stingray127/handwirehotswap/img/matrix/col/0.jpg

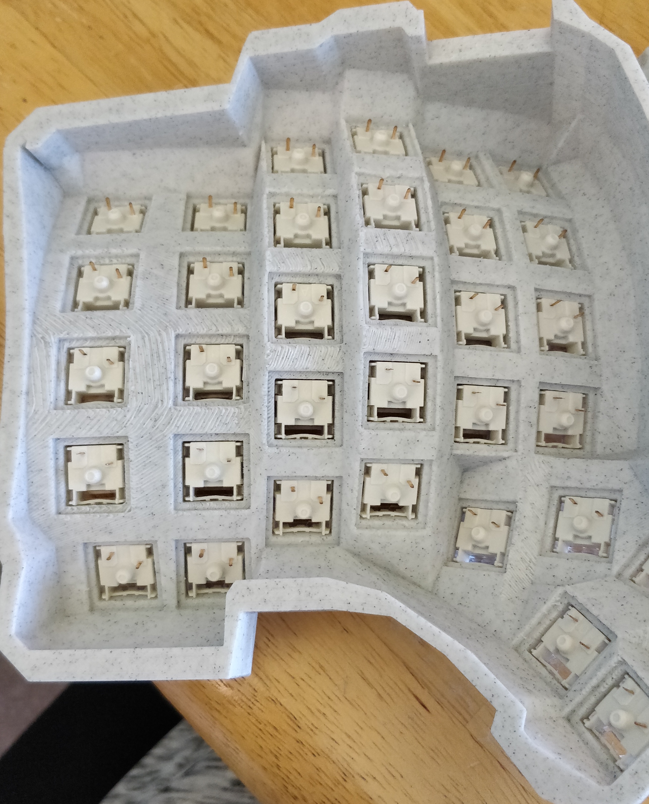
img/matrix/col/0.jpg
