stingray127/handwirehotswap/img/matrix/col/1.jpg

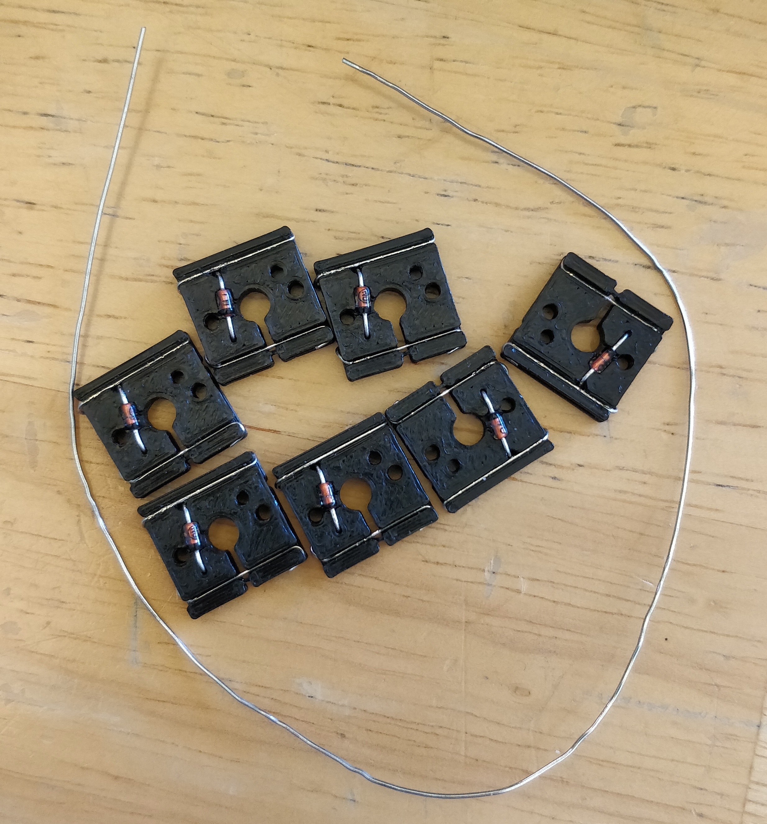
img/matrix/col/1.jpg
