stingray127/handwirehotswap/img/matrix/col/2.jpg

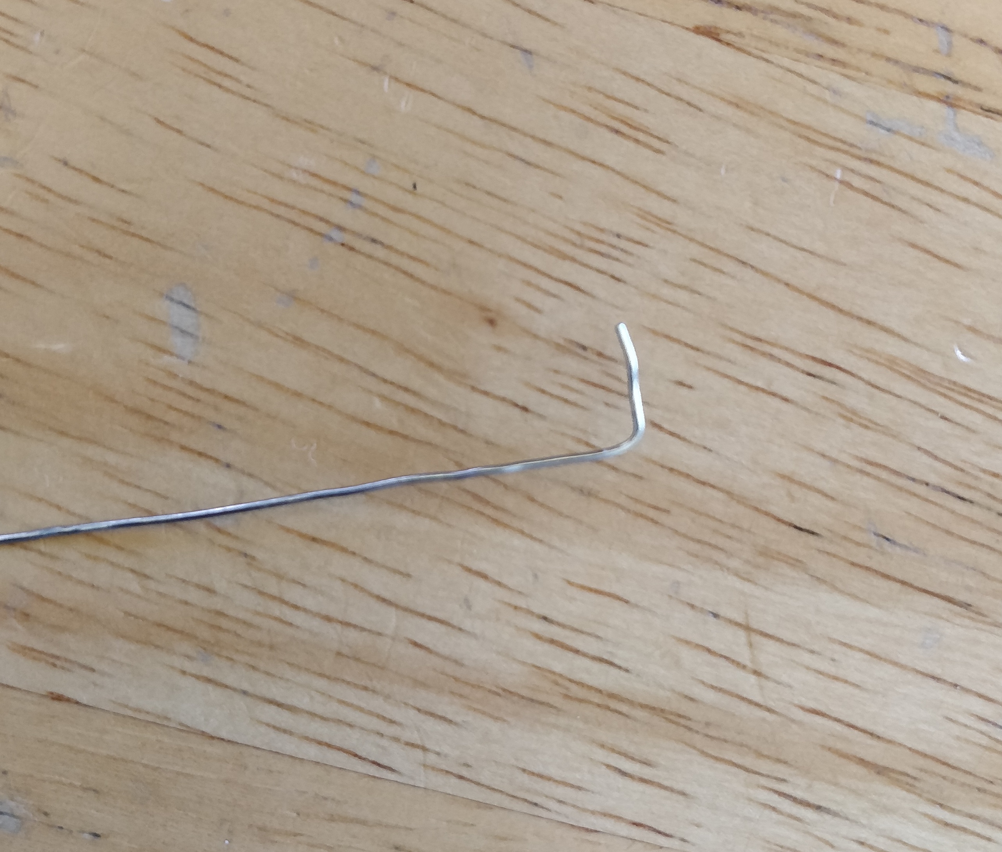
img/matrix/col/2.jpg
