stingray127/handwirehotswap/img/matrix/col/3.jpg

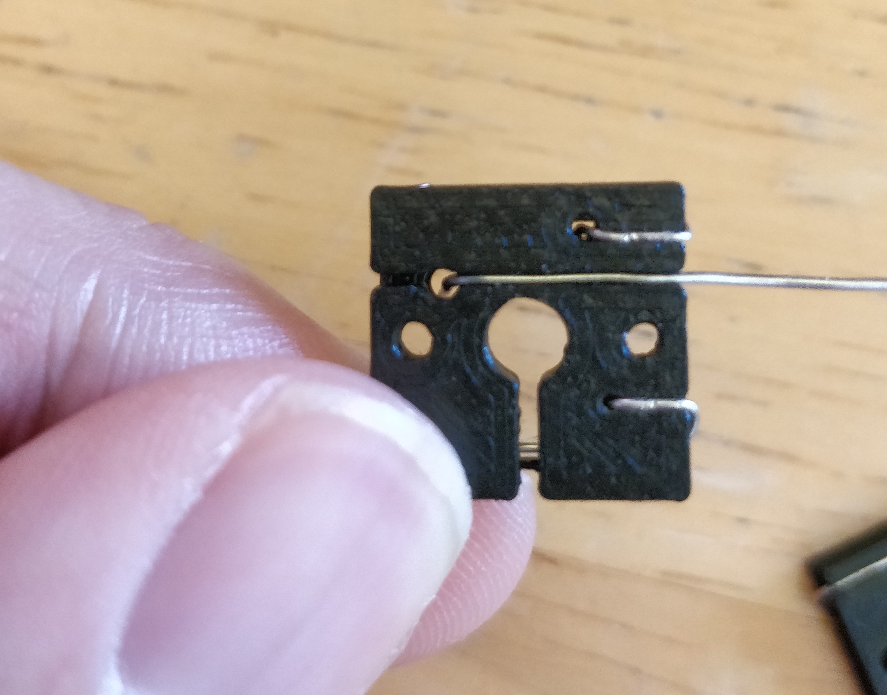
img/matrix/col/3.jpg
