stingray127/handwirehotswap/img/matrix/col/4.jpg

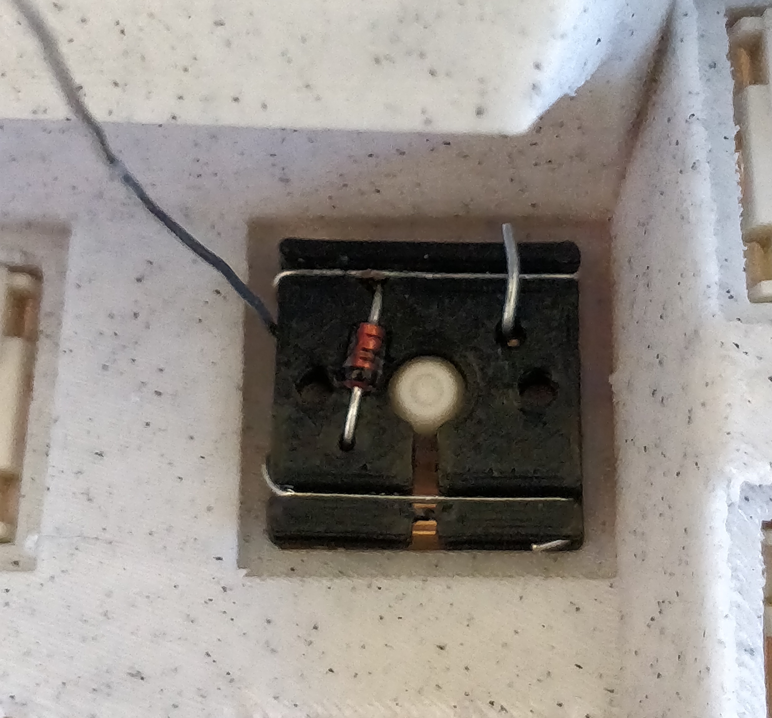
img/matrix/col/4.jpg
