stingray127/handwirehotswap/img/matrix/col/5.jpg

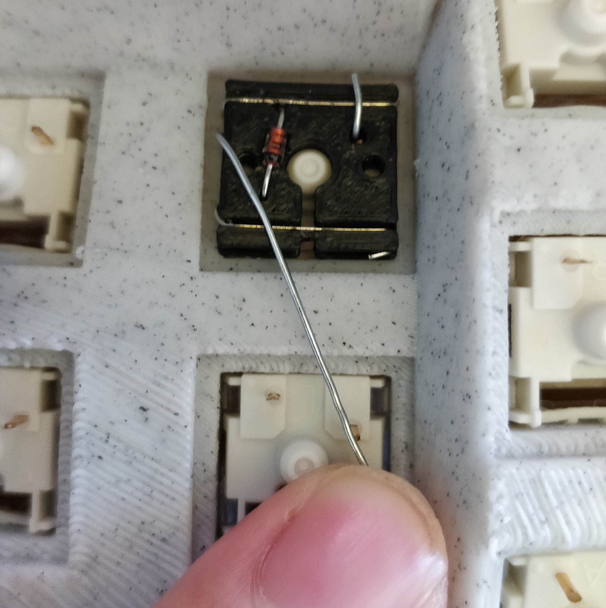
img/matrix/col/5.jpg
