stingray127/handwirehotswap/img/matrix/col/6.jpg

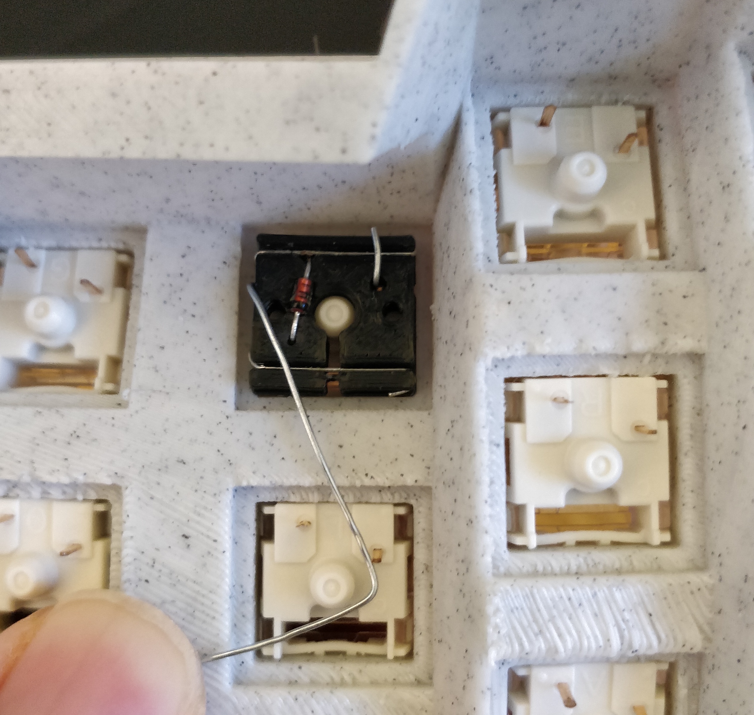
img/matrix/col/6.jpg
