stingray127/handwirehotswap/img/matrix/col/7.jpg

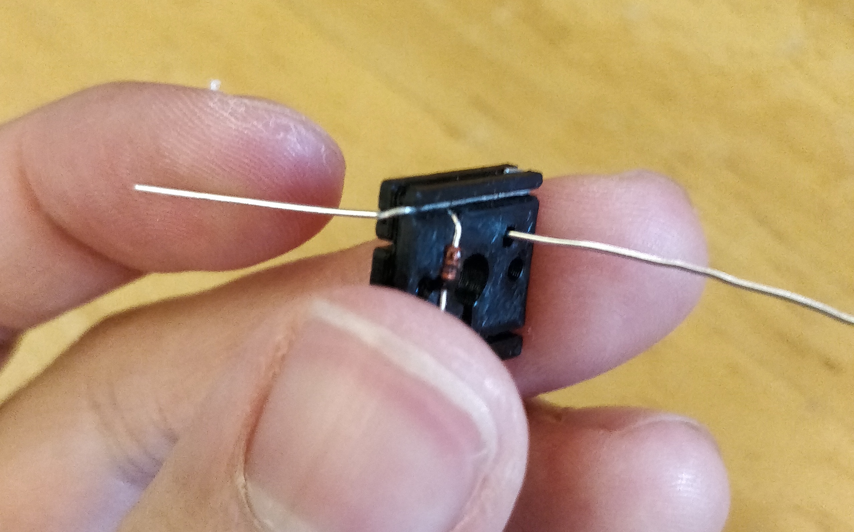
img/matrix/col/7.jpg
