stingray127/handwirehotswap/img/matrix/col/8.jpg

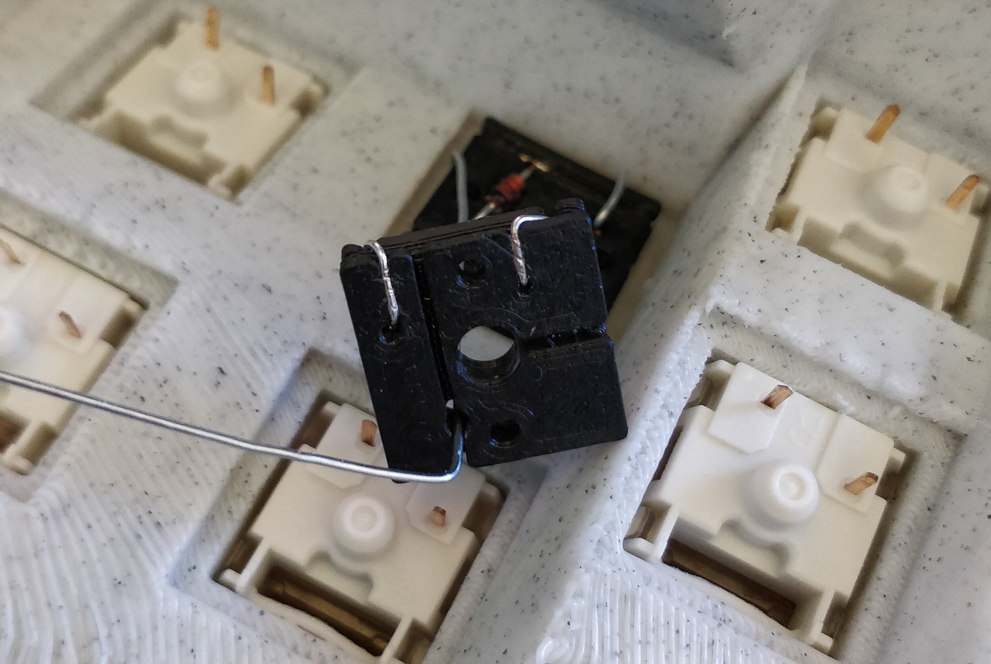
img/matrix/col/8.jpg
