stingray127/handwirehotswap/img/matrix/col/9.jpg

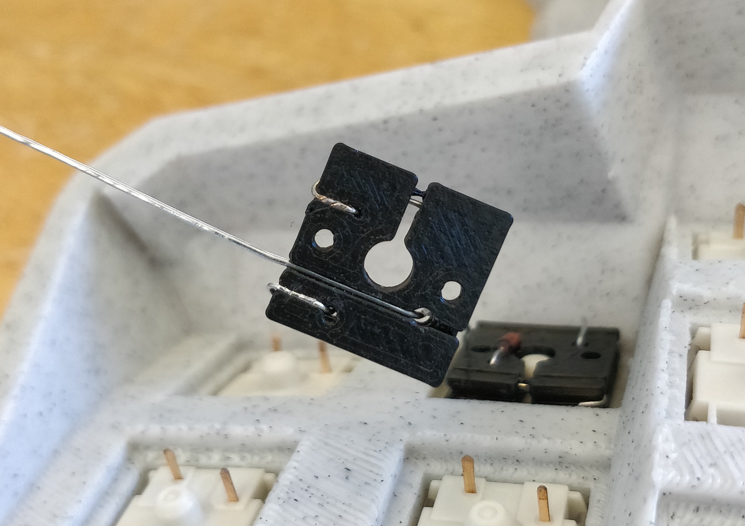
img/matrix/col/9.jpg
