stingray127/handwirehotswap/img/matrix/col/10.jpg

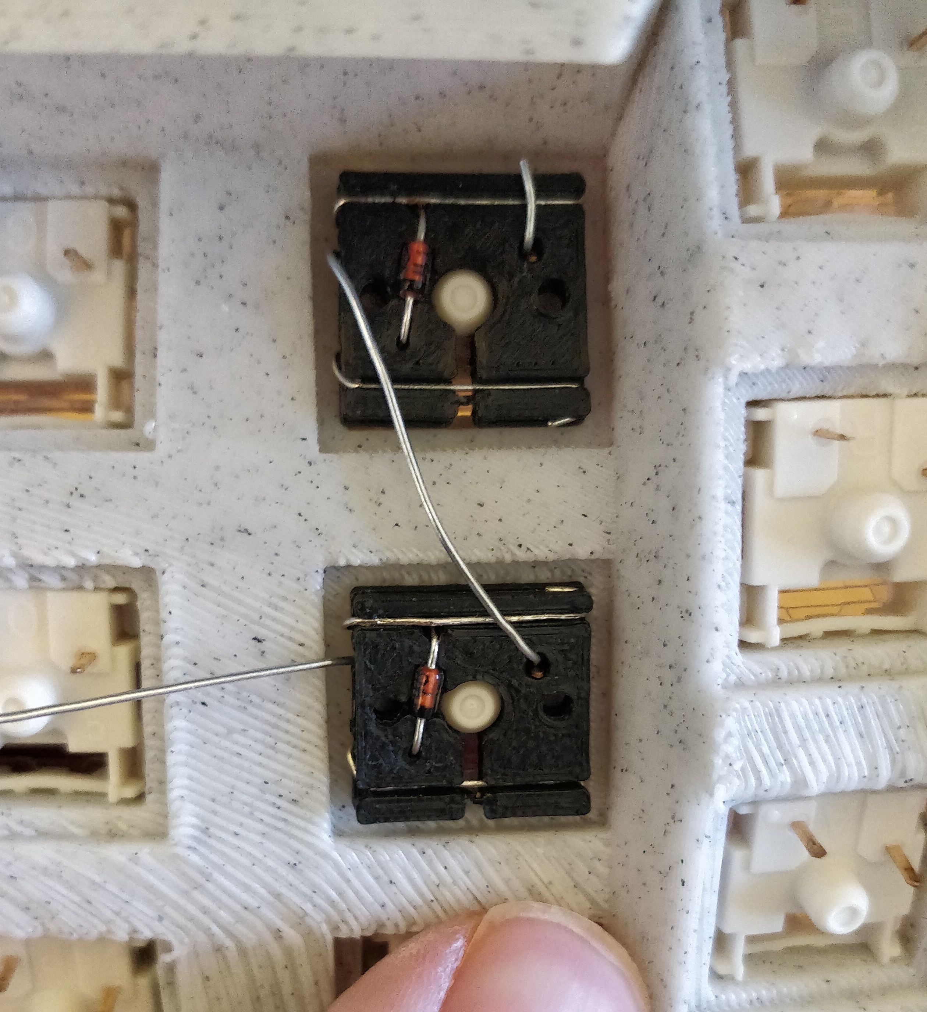
img/matrix/col/10.jpg
