stingray127/handwirehotswap/img/matrix/col/11.jpg

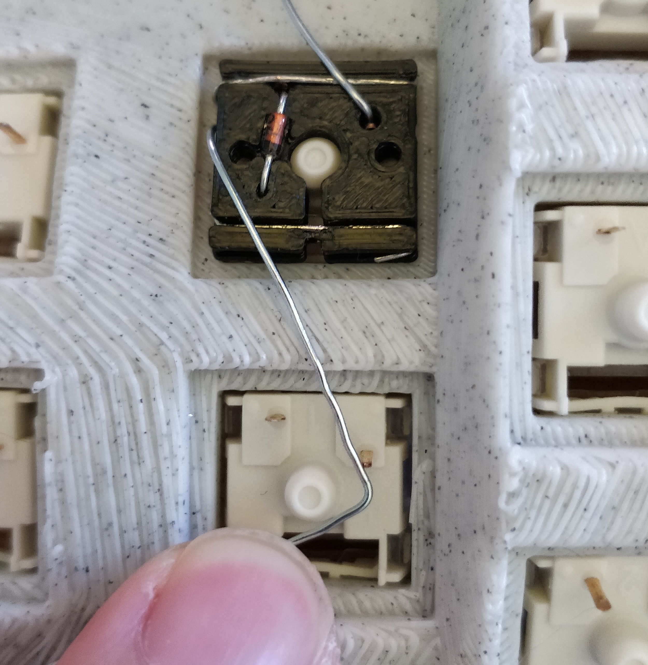
img/matrix/col/11.jpg
