stingray127/handwirehotswap/img/matrix/col/12.jpg

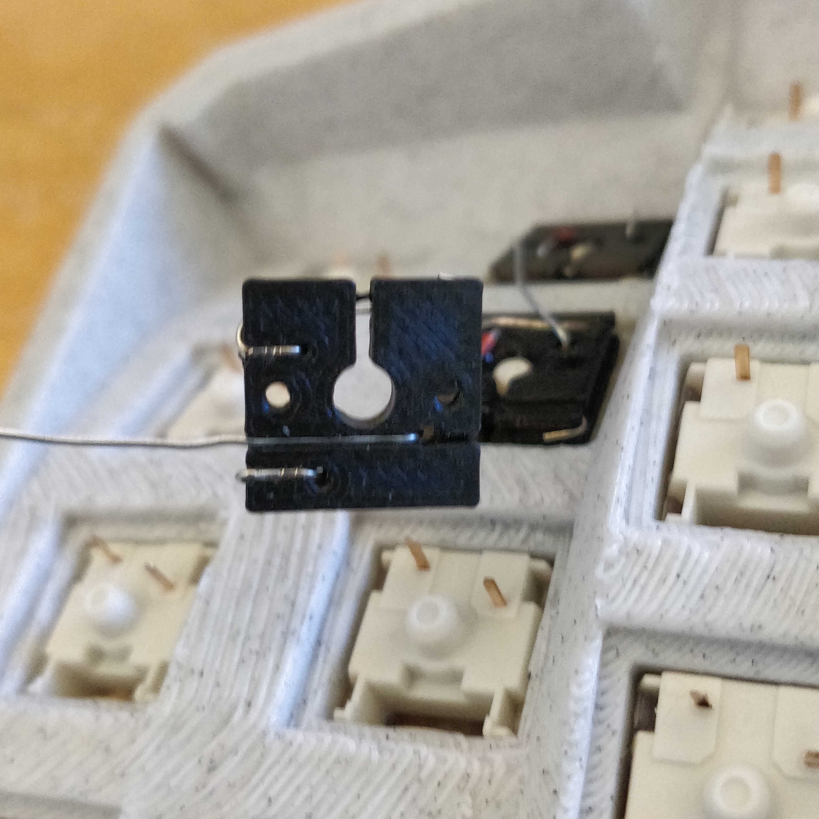
img/matrix/col/12.jpg
