stingray127/handwirehotswap/img/matrix/col/13.jpg

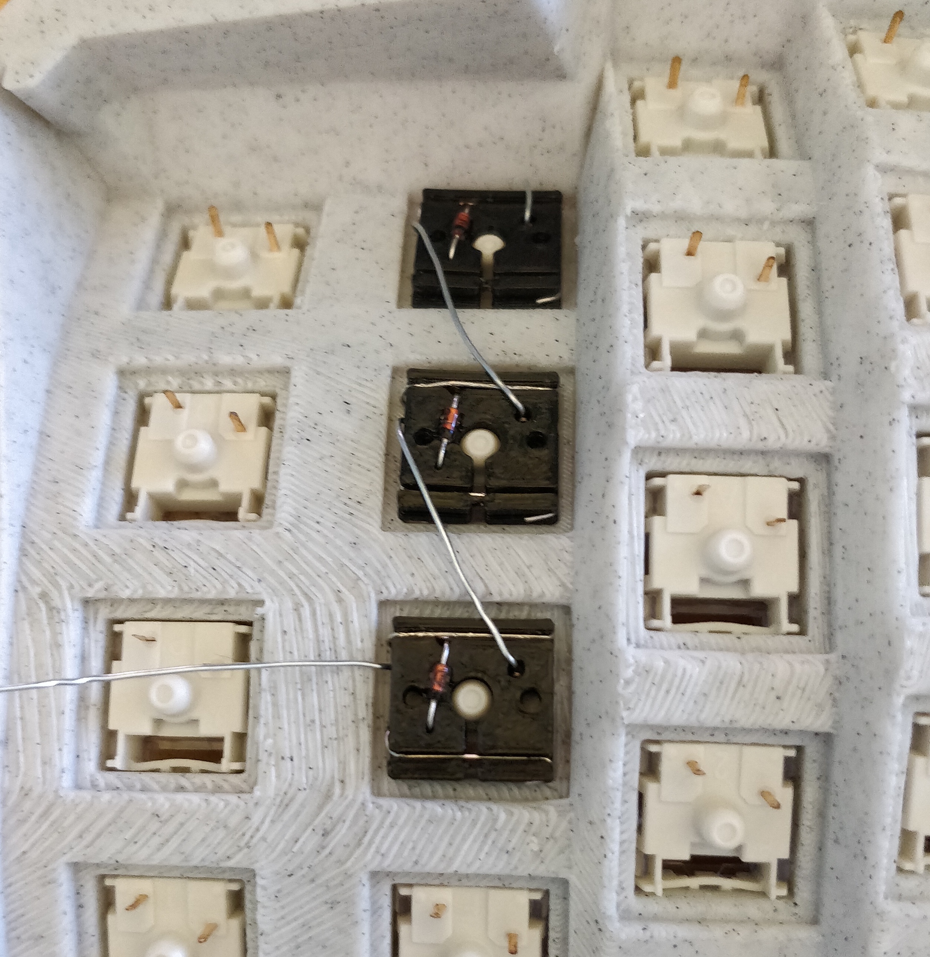
img/matrix/col/13.jpg
