stingray127/handwirehotswap/img/socket/1.jpg

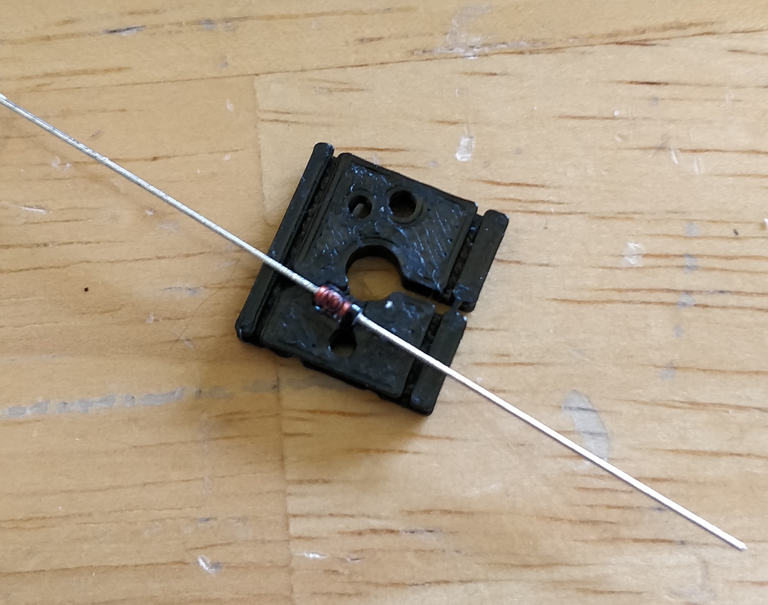
img/socket/1.jpg
