stingray127/handwirehotswap/img/socket/2.jpg

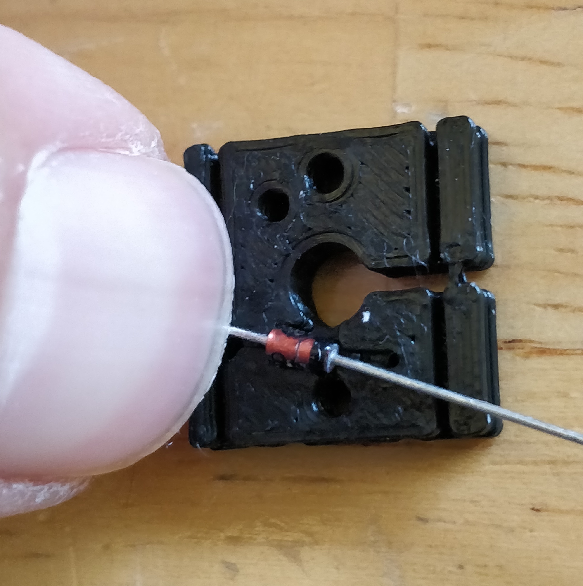
img/socket/2.jpg
