stingray127/handwirehotswap/img/socket/3.jpg

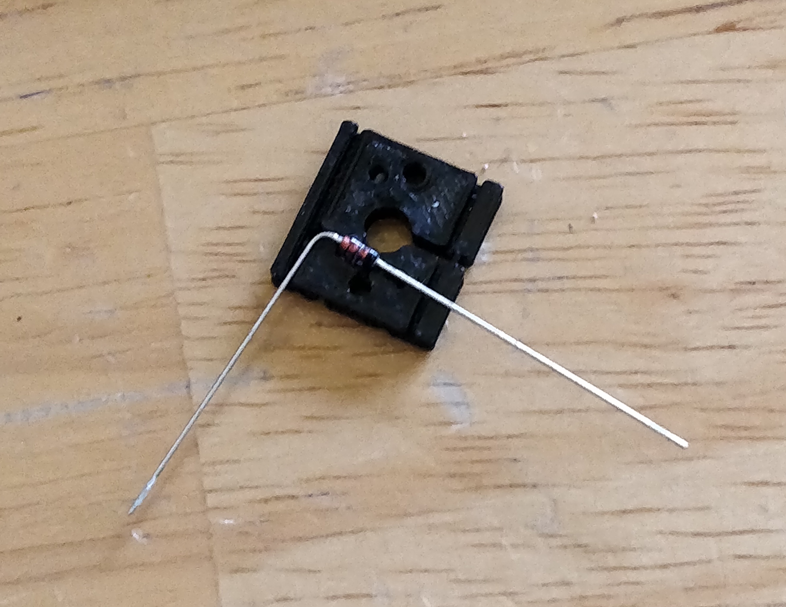
img/socket/3.jpg
