stingray127/handwirehotswap/img/socket/4.jpg

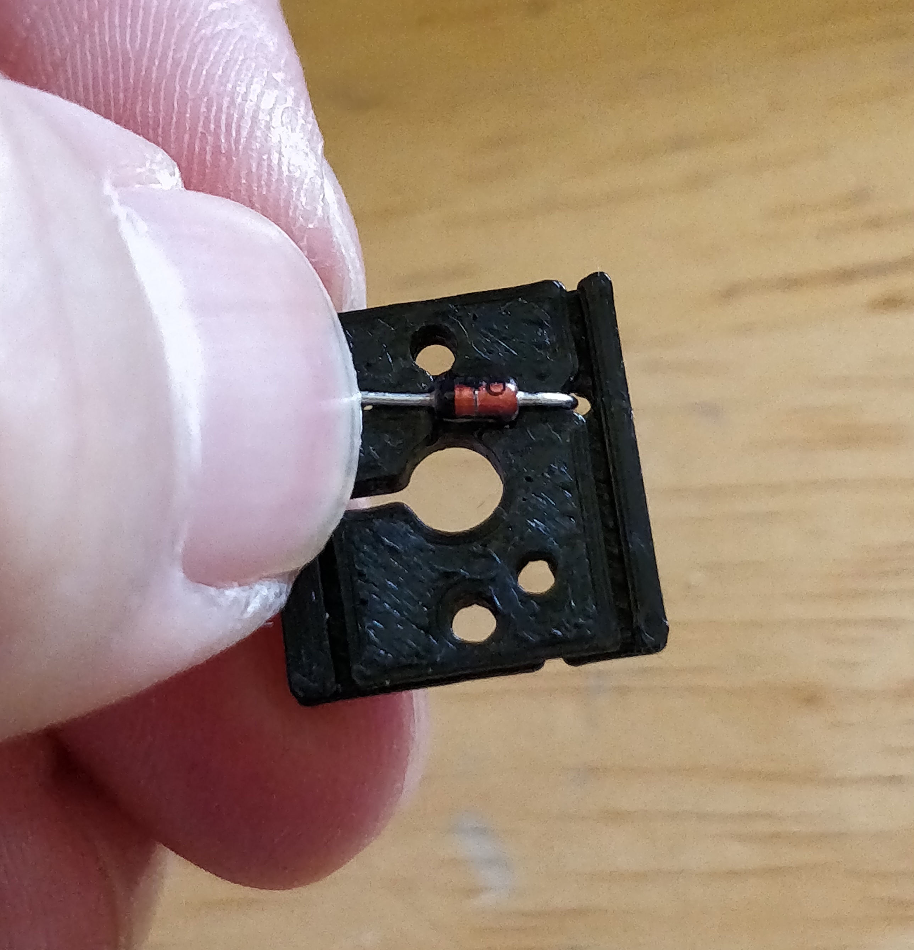
img/socket/4.jpg
