stingray127/handwirehotswap/img/socket/5.jpg

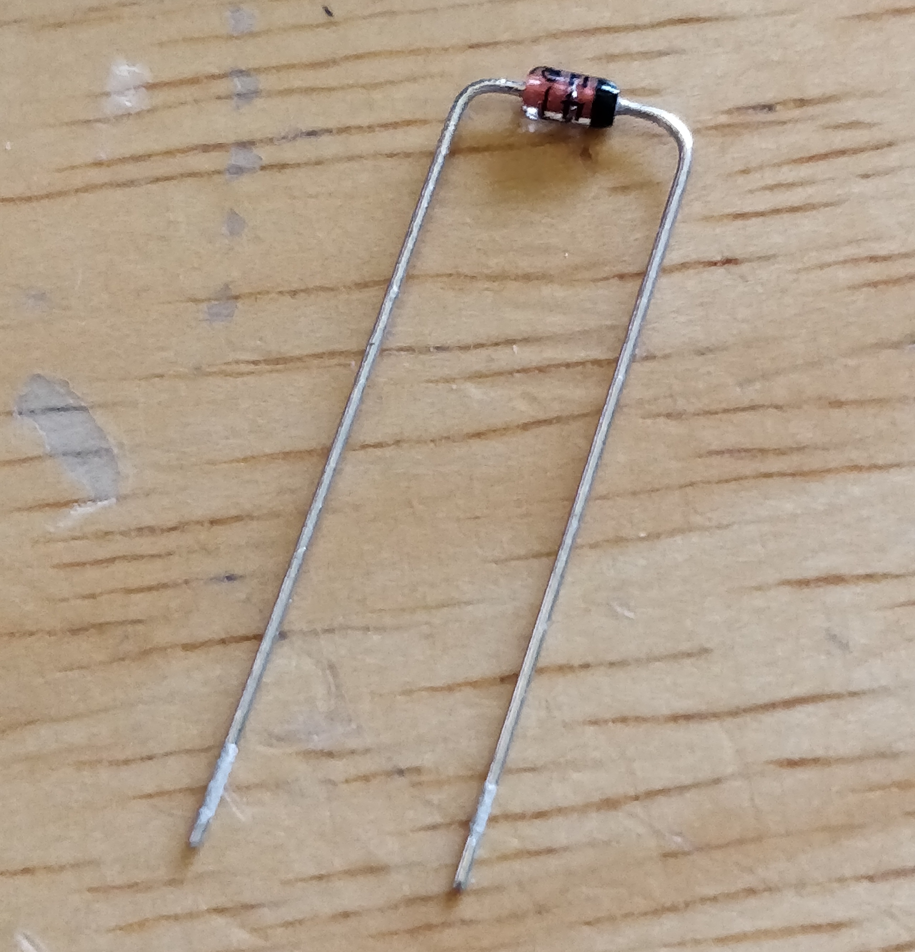
img/socket/5.jpg
