stingray127/handwirehotswap/img/socket/6.jpg

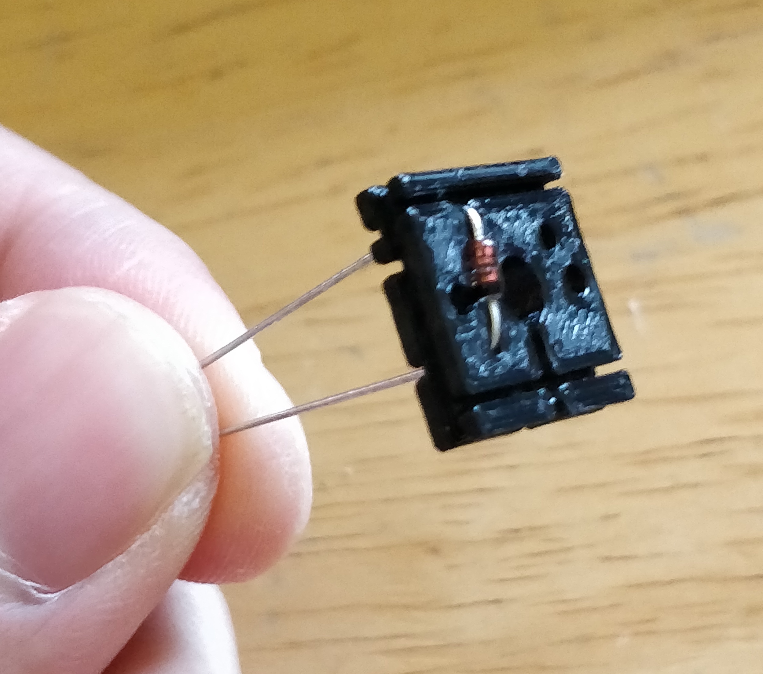
img/socket/6.jpg
