stingray127/handwirehotswap/img/socket/7.jpg

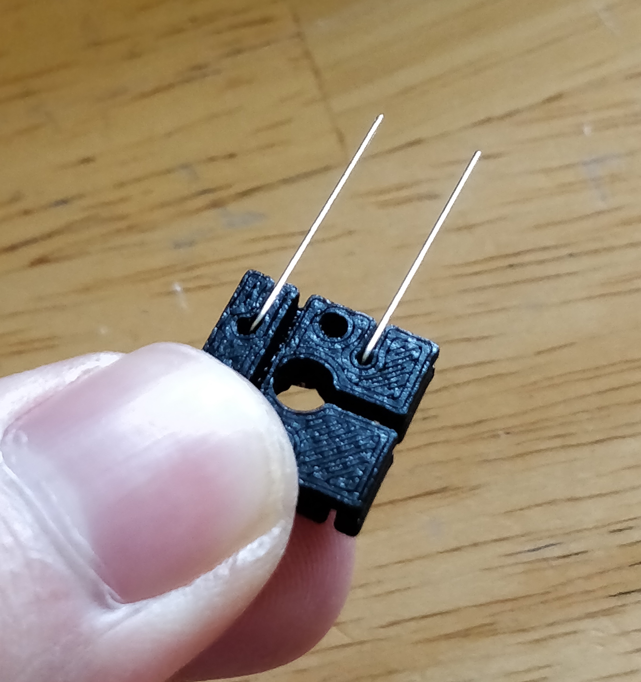
img/socket/7.jpg
