stingray127/handwirehotswap/img/socket/8.jpg

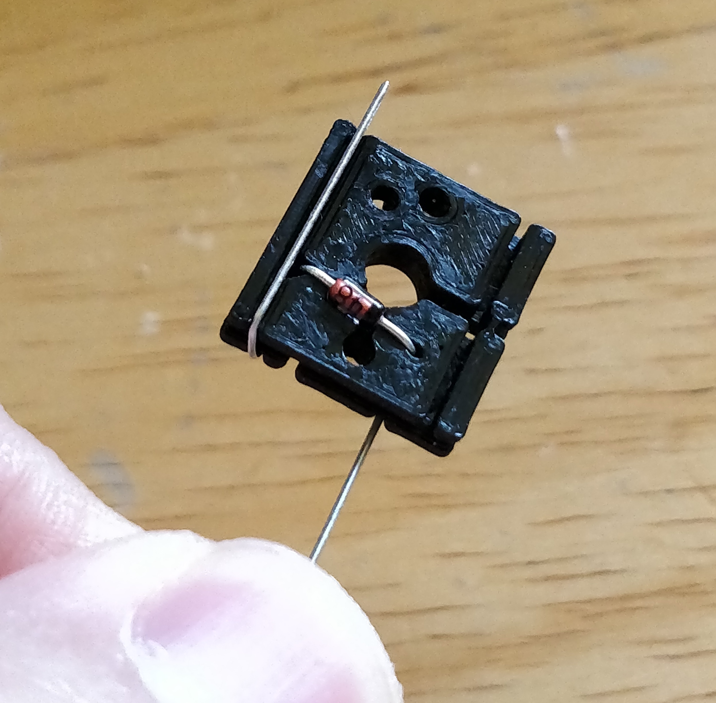
img/socket/8.jpg
