stingray127/handwirehotswap/img/socket/9.jpg

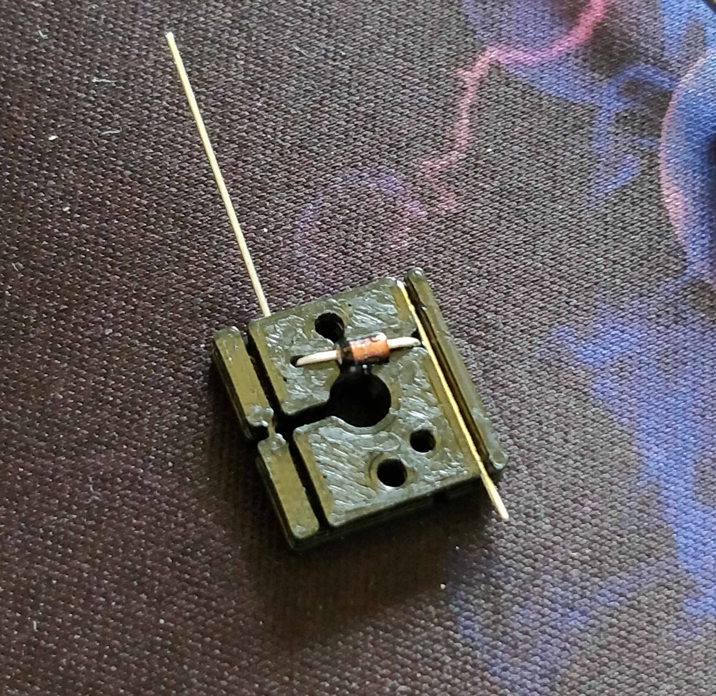
img/socket/9.jpg
