stingray127/handwirehotswap/img/socket/10.jpg

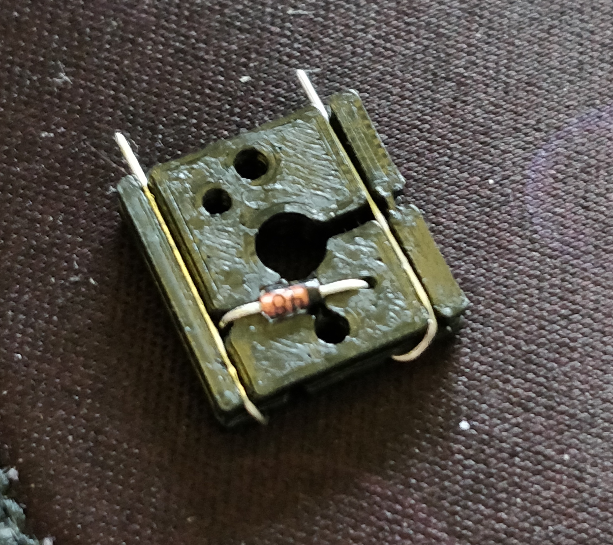
img/socket/10.jpg
