stingray127/handwirehotswap/img/socket/11.jpg

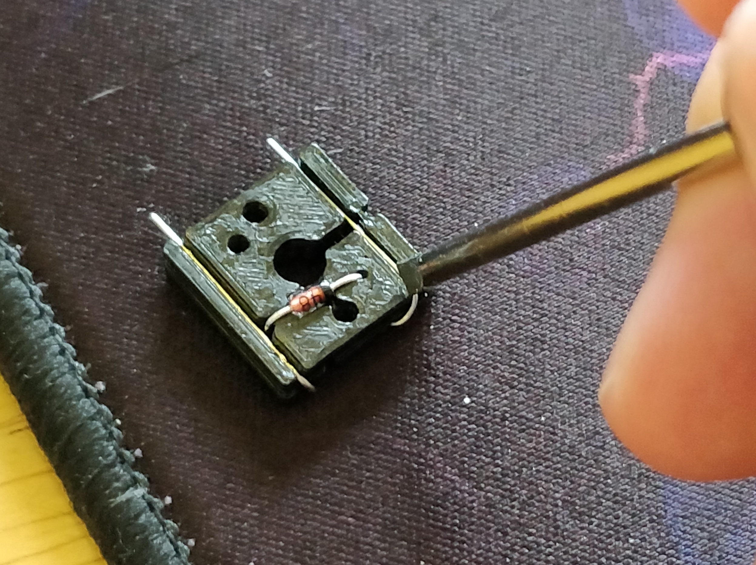
img/socket/11.jpg
