stingray127/handwirehotswap/img/socket/12.jpg

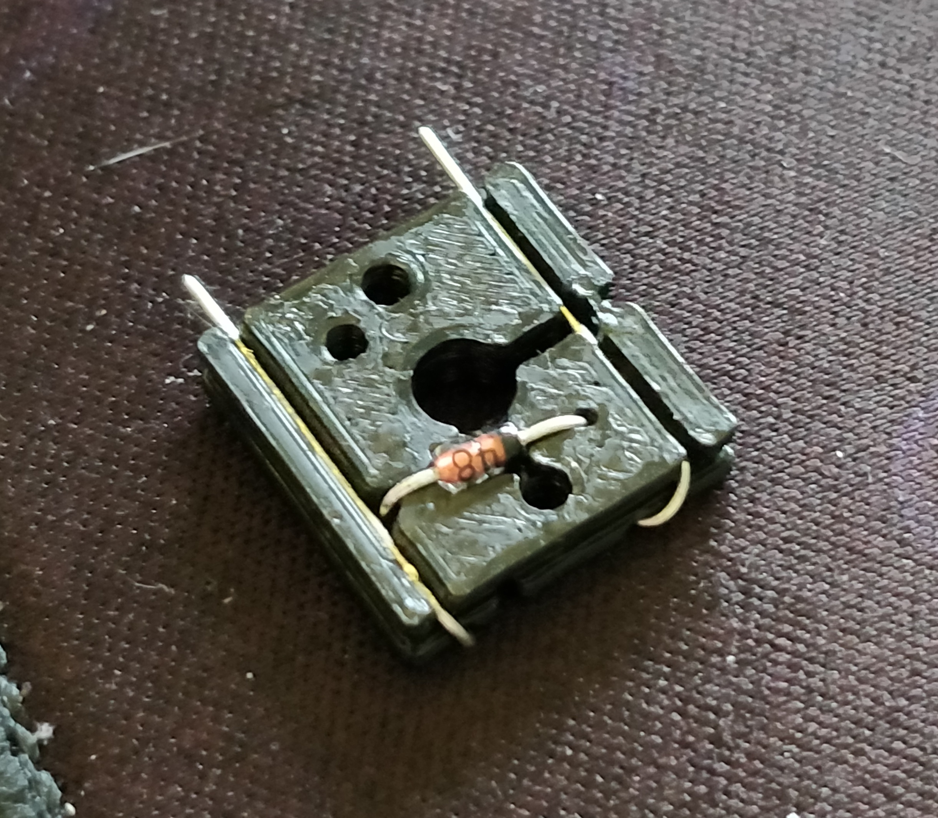
img/socket/12.jpg
