stingray127/handwirehotswap/img/socket/13.jpg

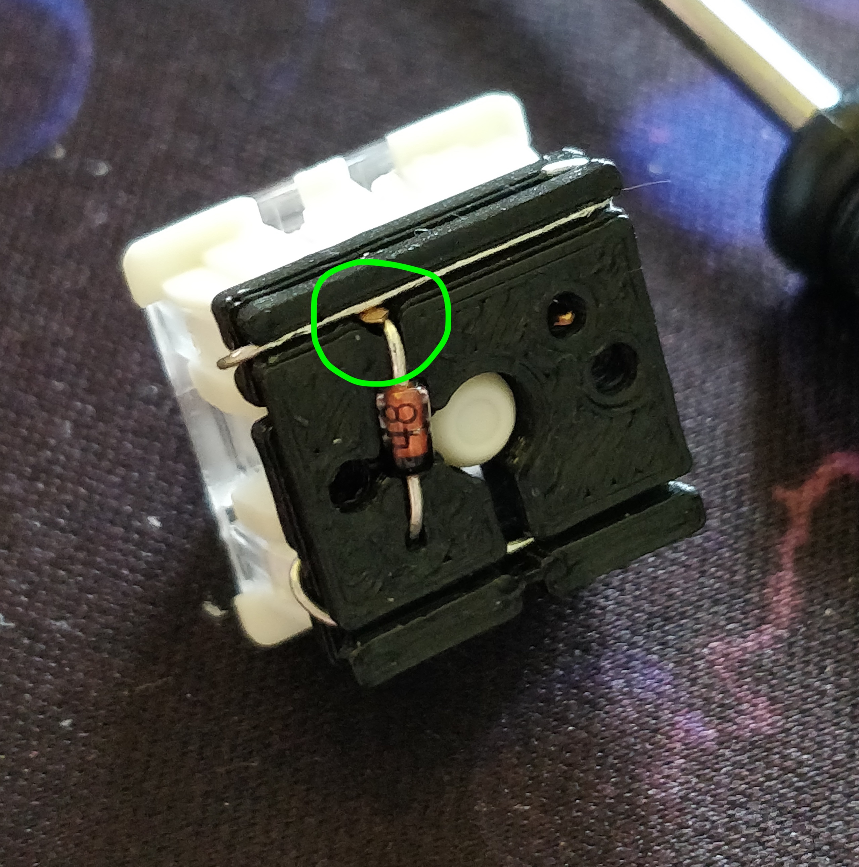
img/socket/13.jpg
