stingray127/handwirehotswap/img/socket/14.jpg

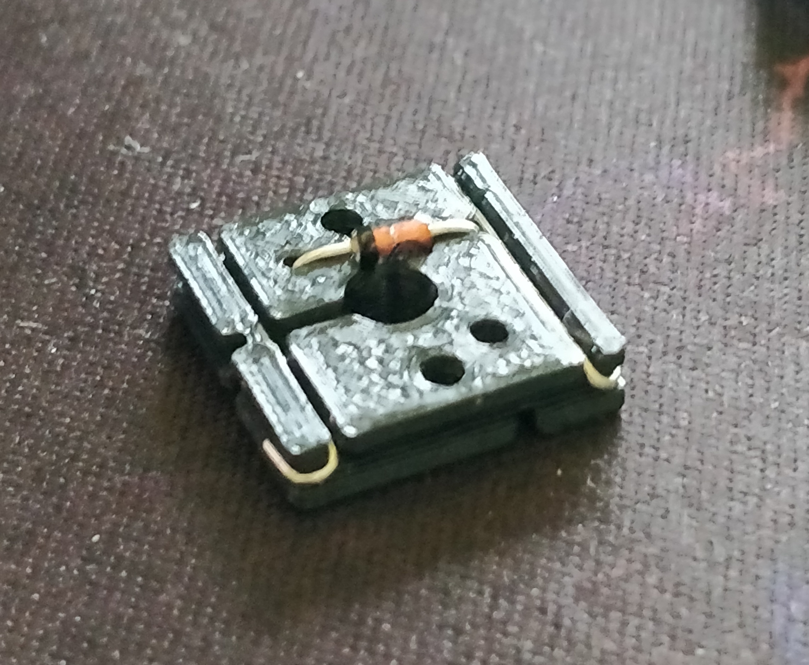
img/socket/14.jpg
